Simon-Hoffmann/SafetyWarnSystem/Sensors/adafruit/RF_Communication_Module/RF_Communication_Module.ino

/**
*	@file 	RF_Communication_Module.ino
*	@author Simon Hoffmann
*	@brief	Main Program start and loop - Select the type of sensor in sensor.h
* @date   10.11.2022
*/

/*-------------------------- I N C L U D E S ----------------------------*/

#include "sensor.h"
#include "debug.h"
#include "rfm.h"

/* ----------- V A R I A B L E S   &  C O N S T A N T S  --------------- */

#define VERSION  "1.0.0"
const int Reset = 14;

/* ------------- F u n c t i o n  P r o t o t y p e s  ----------------- */

/* ----------------------- F U N C T I O N S  -------------------------- */

/**
*	Startup for initialisation
*
*	@param 	none
*	@return none
*/
void setup(void) {
  digitalWrite(Reset, HIGH);
  delay(200);
  pinMode(Reset, OUTPUT);
  #ifdef DEBUG
    Serial.begin(115200);
  #endif
  
  #ifndef HARDWARE_DEBUG
  rfm_init();
  #endif
  sensor_init();
}

/**
*	Main program loop 
*
*	@param 	none
*	@return none
*/
void loop(void) {
  sensor_task();
  //put sensor into sleep state for 1s
  delay(1000);
}
